88markus88/EnvMonitor/EnovMonitor680-Git/src/HelperFunctions.h

/******************************************************
* function prototypes for helper functions
*******************************************************/

void logOut(char* printstring, unsigned int MsgID, unsigned int MsgSeverity);
